myhumankit/Detecteur_de_muons/Electronic models/Versions_Utilisees/Version Pdf des tests Spice/2µS/Muon_V4-4700K-1nF_plot_2µ_d.pdf

0µs | 80µs | 160µs | 240µs | 320µs | 400µs | 480µs | 560µs | 640µs | 720µs | 800µs

0.0V

0.4V

0.8V

1.2V

1.6V

2.0V

2.4V

2.8V

3.2V

3.6V

4.0V

4.4V

V(n003) | V(n002) | V(out_peak_detect)

### --- I:\FRANCOIS\MUON\Muons_V4_a.raw ---
