myhumankit/Detecteur_de_muons/Electronic models/Versions_Utilisees/Version Pdf des tests Spice/2µS/Muon_V4-4700K-22nF_plot_2µ_a.pdf

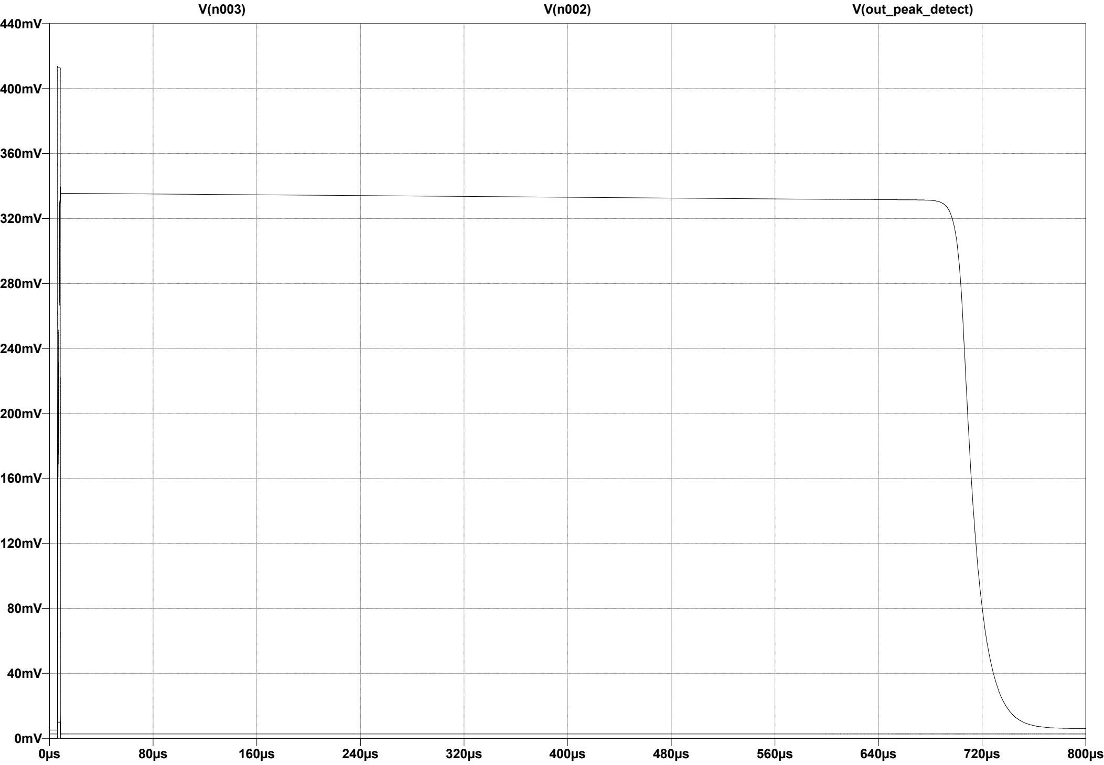
[picture p16: figure]
V(out_peak_detect)

### --- I:\FRANCOIS\MUON\Muons_V4_a.raw ---
