myhumankit/Detecteur_de_muons/Electronic models/Versions_Utilisees/Version Pdf des tests Spice/2µS/Muon_V4-4700K-1nF_2µ_a.pdf

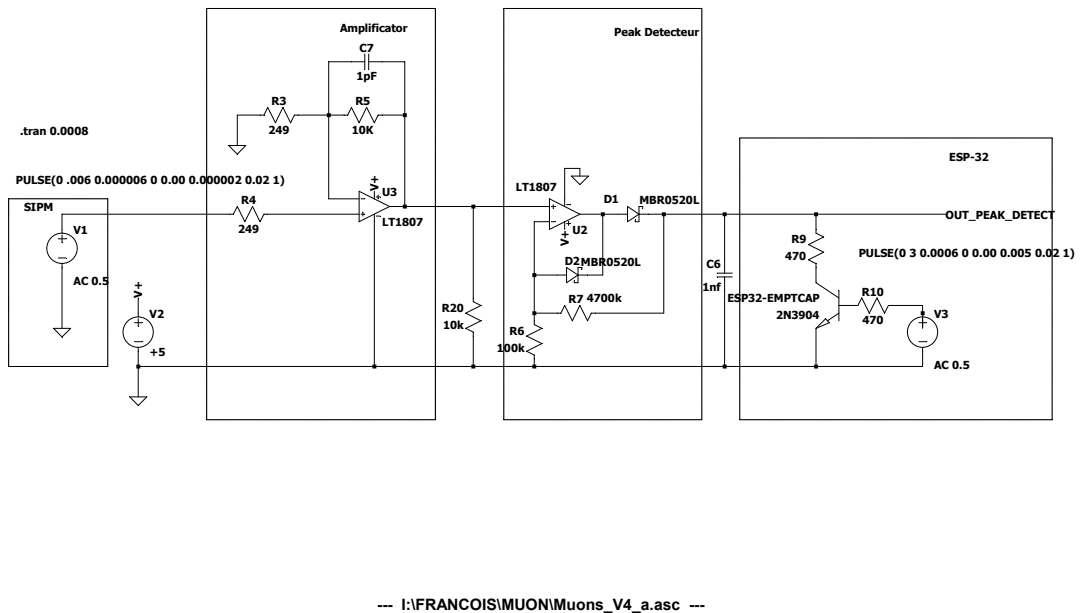
[picture p27: page 1]
