myhumankit/Detecteur_de_muons/Electronic models/Versions_Utilisees/Version Pdf des tests Spice/2µS/Muon_V4-4700K-1nF_Zoom_plot_2µ_c.pdf

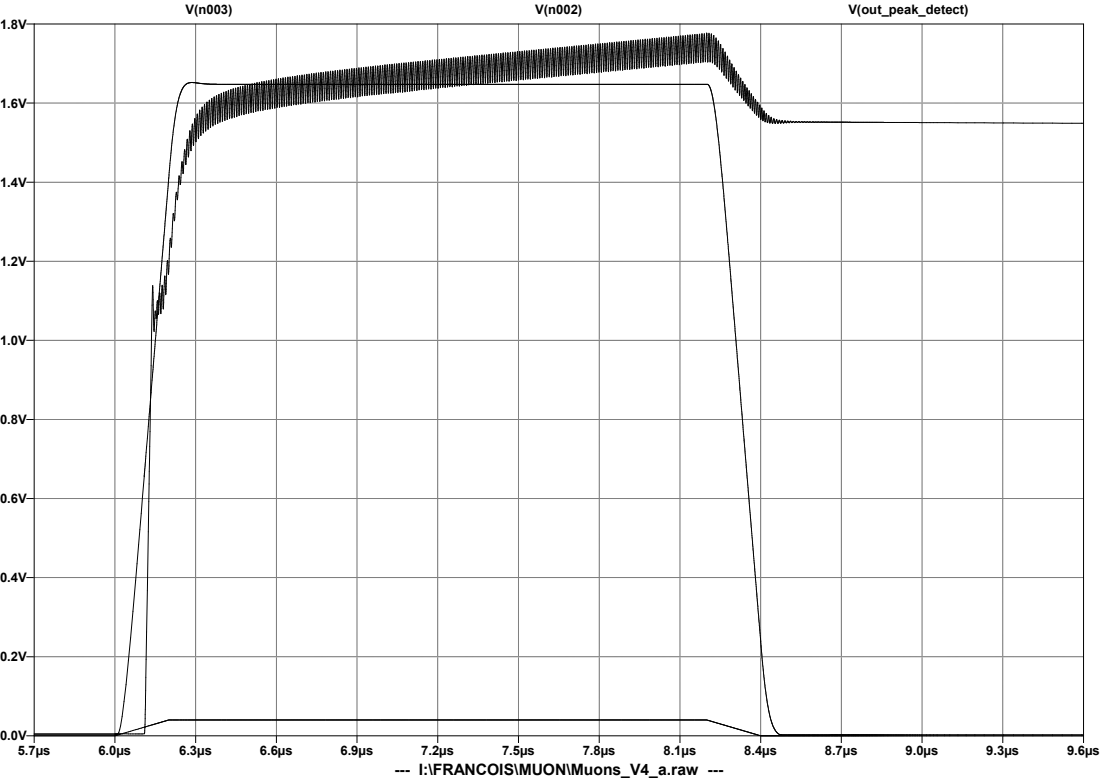
[picture p33: page 1]
V(out_peak_detect)

--- I:\FRANCOIS\MUON\Muons_V4_a.raw ---
