myhumankit/Detecteur_de_muons/Electronic models/Versions_Utilisees/Version Pdf des tests Spice/2µS/Muon_V4-4700K-4.7nF_2µ_d.pdf

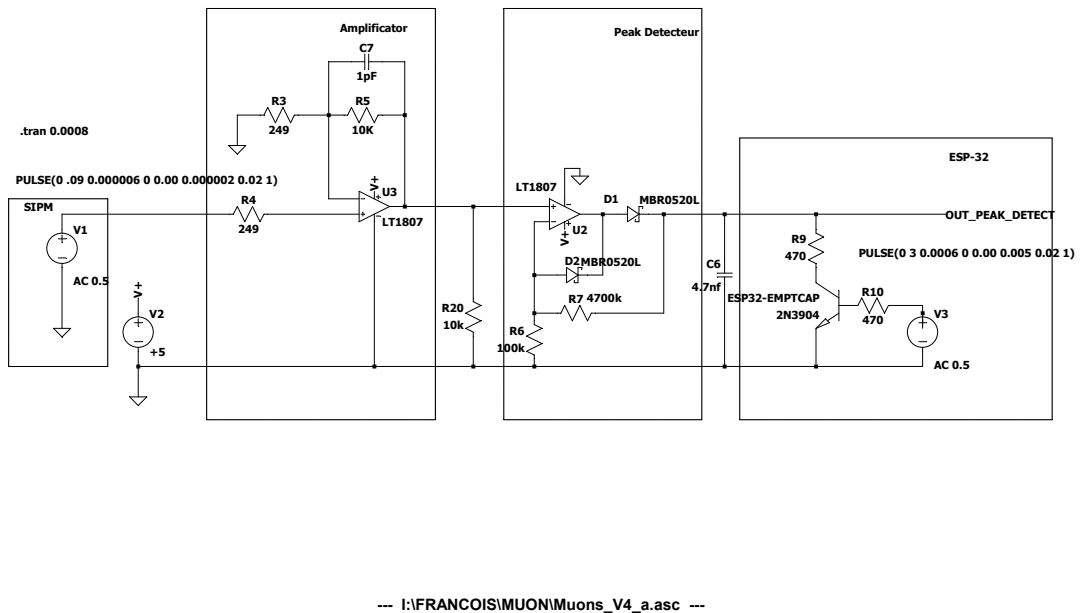
[picture p48: page 1]
