myhumankit/Detecteur_de_muons/Electronic models/Versions_Utilisees/Version Pdf des tests Spice/500nS/Muon_V4-4700K-10nF_b.pdf

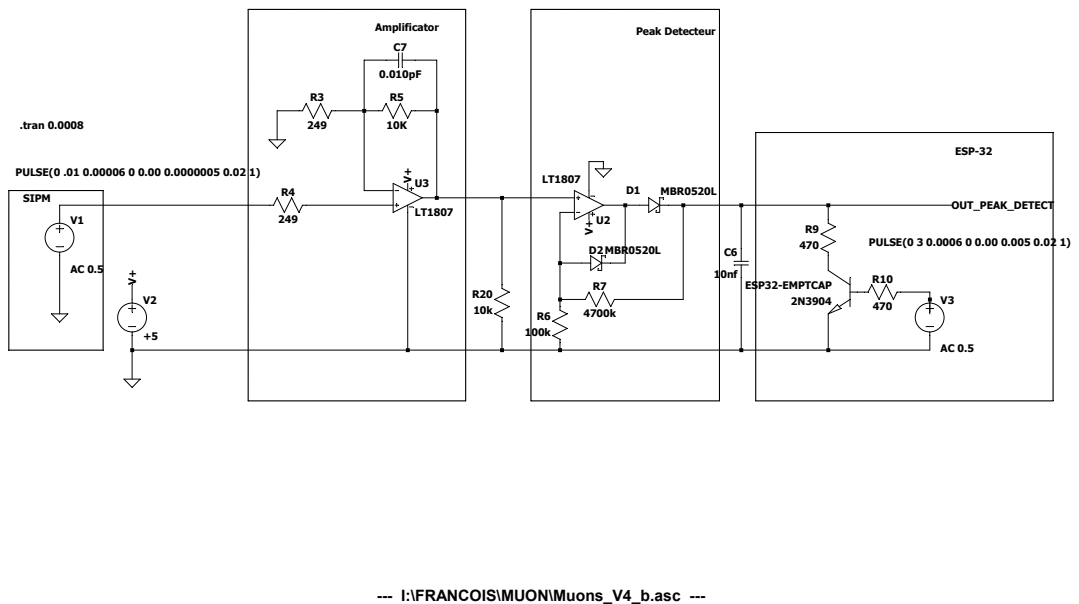
[picture p54: page 1]
