myhumankit/Detecteur_de_muons/Electronic models/Versions_Utilisees/Version Pdf des tests Spice/500nS/Muon_V4-4700K-22nF_plot_a.pdf

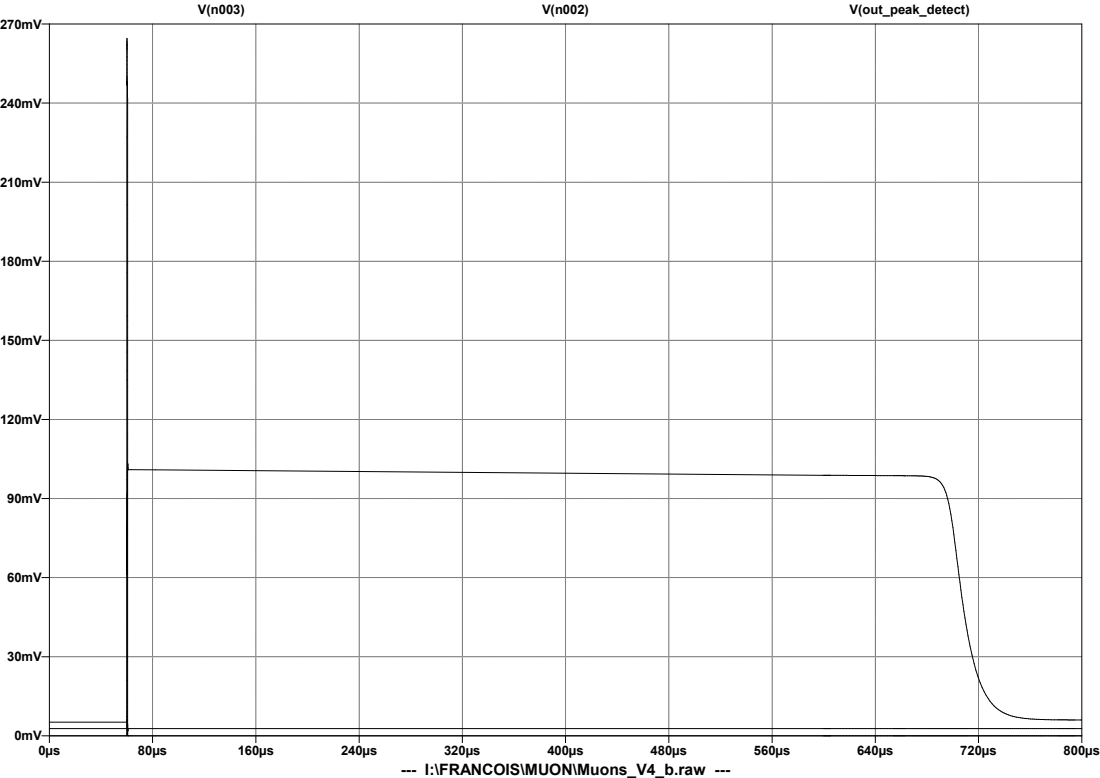
[picture p81: page 1]
V(out_peak_detect)

--- I:\FRANCOIS\MUON\Muons_V4_b.raw ---
