myhumankit/Detecteur_de_muons/Electronic models/Version_Spencer/Muons01.asc

C3: cap; 20nF
C15: cap; 10pF
D1: schottky; BAT54
D2: schottky; BAT54
R1: res; 100k
R2: res; 24.9k
R5: res; 100K
R30: res; 10K
R31: res; 249
R33: res; 10k
R37: res; 249
U2: LT1807
U3: LT1807
V1: voltage; PULSE(0 .05 0.0001 0 0.001 0.0001 0.1 5); AC 0.2
V2: voltage; +5
Named nets: 0, V+, OUT2
.tran .5
