myhumankit/Detecteur_de_muons/Electronic models/Version_Spencer/Muons02.asc

C3: cap; 1nF
D1: schottky; BAT54
D2: schottky; BAT54
R1: res; 100k
R5: res; 100K
R30: res; 1k
R31: res; 100
R37: res; 1k
U1: LT6201
U4: LT6201
V1: voltage; PULSE(0 .2 0.0001 0 0.0001 0.00001 0.1 5); AC 0.2
V2: voltage; +5
Named nets: 0, V+, OUT2
.tran .5
