myhumankit/Detecteur_de_muons/Electronic models/Versions_Utilisees/Muons_moyenne_01.asc

C3: cap; 4.7nf
C15: cap; 1pF
D1: schottky; MBR0520L
D2: schottky; MBR0520L
Q1: npn; 2N3904
R1: res; 4700k
R2: res; 100k
R4: res; 249
R5: res; 0
R30: res; 10K
R31: res; 249
R33: res; 10k
R37: res; 249
U2: LT1807
U3: LT1807
V1: voltage; PULSE(0 .006 0.00006 0 0.00 0.0000005 0.02 1); AC 0.5
V2: voltage; +5
V3: voltage; PULSE(0 3 0.0006 0 0.00 0.005 0.02 1); AC 0.5
Named nets: 0, V+, OUT2
.tran 0.0008
