myhumankit/Detecteur_de_muons/Electronic models/Versions_Utilisees/Muons_V4_a.asc

C1: cap; 1pF
C6: cap; 1nf
C7: cap; 0.010pF
D1: schottky; MBR0520L
D2: schottky; MBR0520L
ESP32-EMPTCAP: npn; 2N3904
R1: res; 1k
R2: res; 6800k
R3: res; 249
R4: res; 249
R5: res; 10K
R6: res; 100k
R7: res; 6800k
R9: res; 470
R10: res; 470
R20: res; 10k
U2: LT1807
U3: LT1807
V1: voltage; PULSE(0 .008 0.000006 0 0.00 0.0000001 0.02 5); AC 0.5
V2: voltage; +5
V3: voltage; PULSE(0 3 0.0006 0 0.00 0.005 0.02 3); AC 0.5
Named nets: 0, V+, OUT_PEAK_DETECT
.tran 0.1008
Peak Detecteur
Amplificator
ESP-32
SIPM
