myhumankit/Detecteur_de_muons/Electronic models/Versions_Utilisees/Muons_V4_d.asc

C1: cap; 0.01nF
C3: cap; 1nF
C7: cap; 10pF
ESP32-EMPTCAP: npn; 2N3904
R1: res; 100K
R2: res; 10k
R3: res; 249
R4: res; 249
R5: res; 10K
R6: res; 10k
R7: res; 10k
R8: res; 82k
R9: res; 470
R10: res; 470
R11: res; 100k
R12: res; 82k
R13: res; 82k
R14: res; 249
U2: LTC6752
U3: LT1807
U4: ADG841
U5: AD8618
V1: voltage; PULSE(0 .04 0.00006 0 0.00 0.0000005 0.02 1); AC 0.5
V2: voltage; +5
V3: voltage; PULSE(0 3 0.0006 0 0.00 0.05 0.02 1); AC 0.5
Named nets: 0, V+, OUT_PEAK_DETECT
.tran 0.0008
Peak Detecteur
Amplificator
ESP-32
SIPM
